icamaster/Pintry/Simulations/SIA483DJ_test/PowerMux.asc

C3: cap; 100nF
C5: cap; 100nF
M1: pmos; SIA483DJ
M2: pmos; SIA483DJ
M3: nmos; RJK005N03
M4: nmos; RJK005N03
M5: nmos; RJK005N03
M6: pmos; SIA483DJ
M7: pmos; SIA483DJ
R1: res; 47k
R2: res; 160k
R3: res; 47k
R4: res; 47k
R5: res; 2.4
R6: res; 47k
R7: res; 47k
R8: res; 1k
R9: res; 1k
R10: res; 47k
R11: res; 1k
R12: res; 1k
R13: res; 47k
R14: res; 47k
U3: LT1018
V1: voltage; PWL(0 12V 2s 12V 2.00000001s 0V)
V2: voltage; 12V
V3: voltage; 3.3V
Named nets: 0, V1, V2, 3V3
;dc V2 0 -5 10m V1 -2 -3 0.5
.lib SiA483DJ_PS.LIB
.lib SiA483DJ_PS_RC.lib
;op
Place the symbol for a pmos transistor.
CTRL rigth-mouse-click on the placed symbol.
A dialog window will pop-up.
Change Prefix:MP to Prefix:X
.include BZX384-B13.prm
.tran 5s startup
