icamaster/Pintry/Simulations/SIA483DJ_test/SIA483DJ_test.asc

C1: cap; 1000µF
C2: cap; 1000µF
C3: cap; 2.2µ
D1: zener; BZX384-B13
D2: zener; BZX384-B13
D3: zener; BZX384-B13
M1: pmos; SIA483DJ
M2: pmos; SIA483DJ
M3: pmos; SIA483DJ
Q1: pnp; BC856B
Q2: pnp; BC856B
Q3: pnp; BC856B
R1: res; 100
R2: res; 4k7
R3: res; 100k
R4: res; 4.7k
R5: res; 2
R6: res; 4k7
R7: res; 100k
R8: res; 4.7k
R9: res; 2
R10: res; 4k7
R11: res; 10k
R12: res; 4.7k
V1: voltage; 12.5V
V2: voltage; 12.5V
V3: voltage; PULSE(0 25V 0 1s 1s 1s 6s)
Named nets: 0, Limit, NoLimit
;dc V2 0 -5 10m V1 -2 -3 0.5
.lib SiA483DJ_PS.LIB
.lib SiA483DJ_PS_RC.lib
;op
Place the symbol for a pmos transistor.
CTRL rigth-mouse-click on the placed symbol.
A dialog window will pop-up.
Change Prefix:MP to Prefix:X
.tran 10m startup
.include BZX384-B13.prm
;tran 500u startup
.meas CurrLim MAX -I(V2) FROM 0us TO 10ms
